Discovery-Tr/NodeMCU_ve_3D_Yazici_Ile_RC_Tank_Yapimi/Foto/Rc Speed Tank (1).jpg

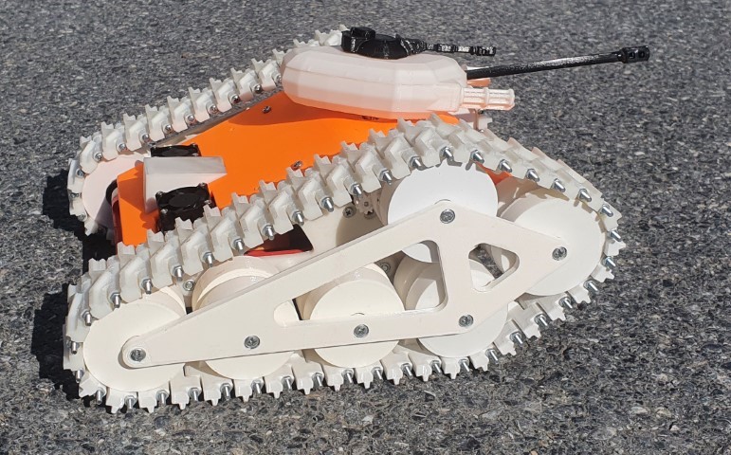
Foto/Rc Speed Tank (1).jpg
