Discovery-Tr/NodeMCU_ve_3D_Yazici_Ile_RC_Tank_Yapimi/Foto/Rc Speed Tank (3).jpeg

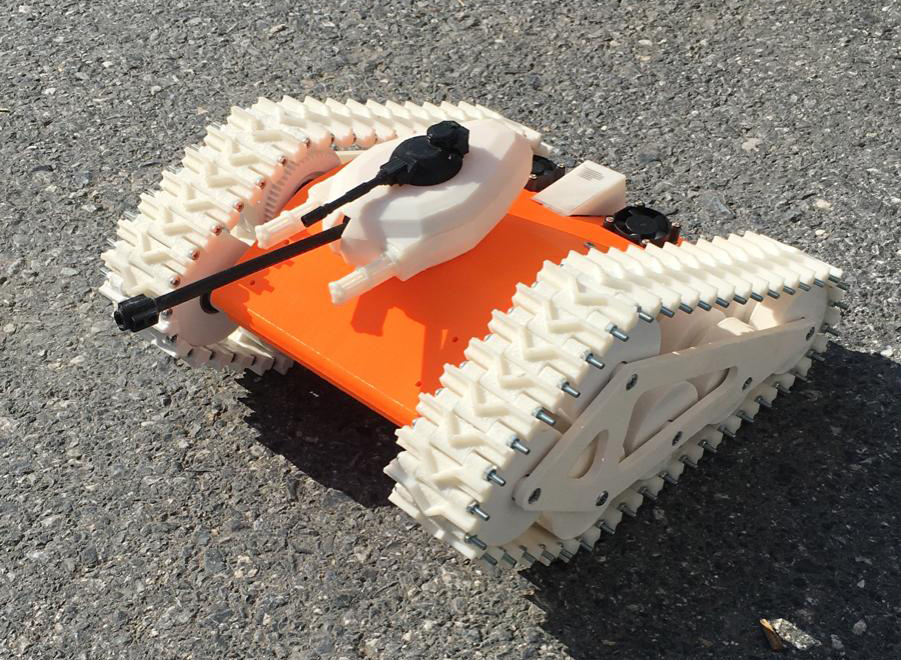
Foto/Rc Speed Tank (3).jpeg
