Discovery-Tr/NodeMCU_ve_3D_Yazici_Ile_RC_Tank_Yapimi/3d/Gövde/Palet Dişlisi.stl

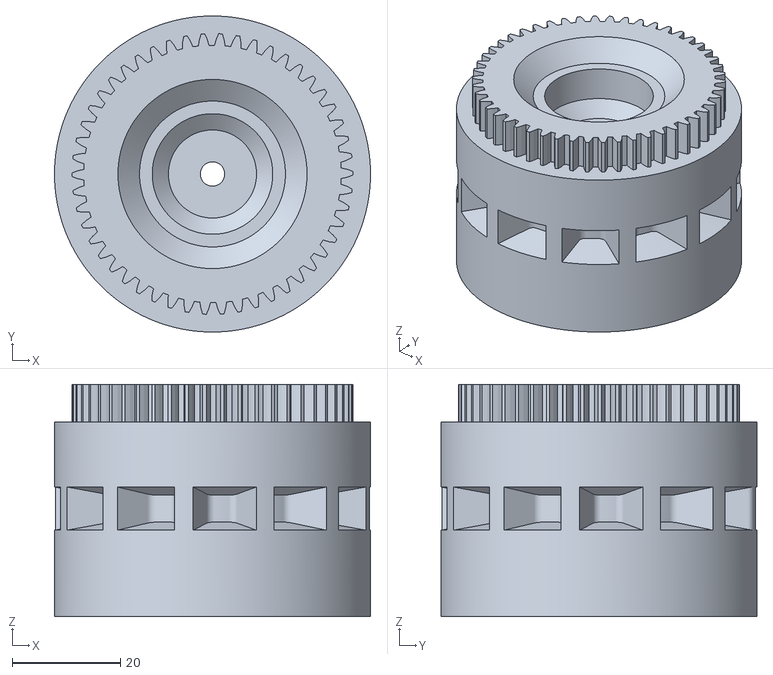
[picture p24: CAD file, 2021-06-29]
3d/Gövde/Palet Dişlisi.stl
58.5 x 58.5 x 43.0
