Discovery-Tr/NodeMCU_ve_3D_Yazici_Ile_RC_Tank_Yapimi/3d/Gövde/Taban Arka.stl

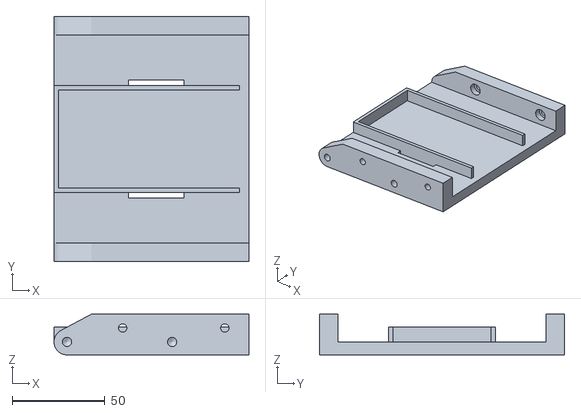
[picture p25: CAD file, 2021-06-29]
3d/Gövde/Taban Arka.stl
105.0 x 132.0 x 22.0
