Discovery-Tr/NodeMCU_ve_3D_Yazici_Ile_RC_Tank_Yapimi/3d/Gövde/motor_disli.stl

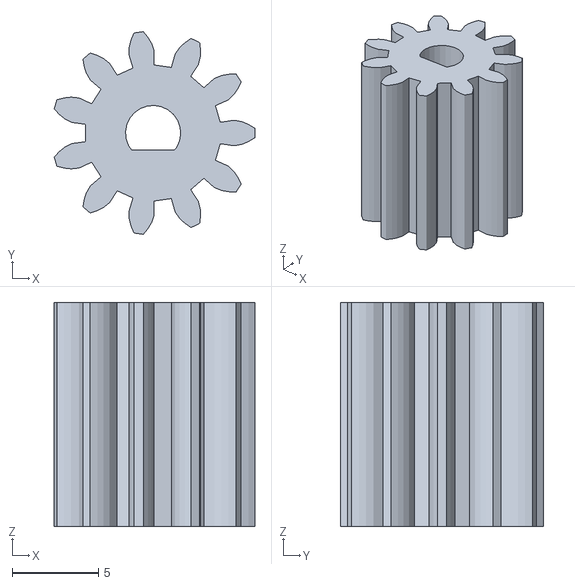
[picture p26: CAD file, 2021-06-29]
3d/Gövde/motor_disli.stl
11.6 x 11.8 x 13.0
