Discovery-Tr/NodeMCU_ve_3D_Yazici_Ile_RC_Tank_Yapimi/3d/Gövde/burun.stl

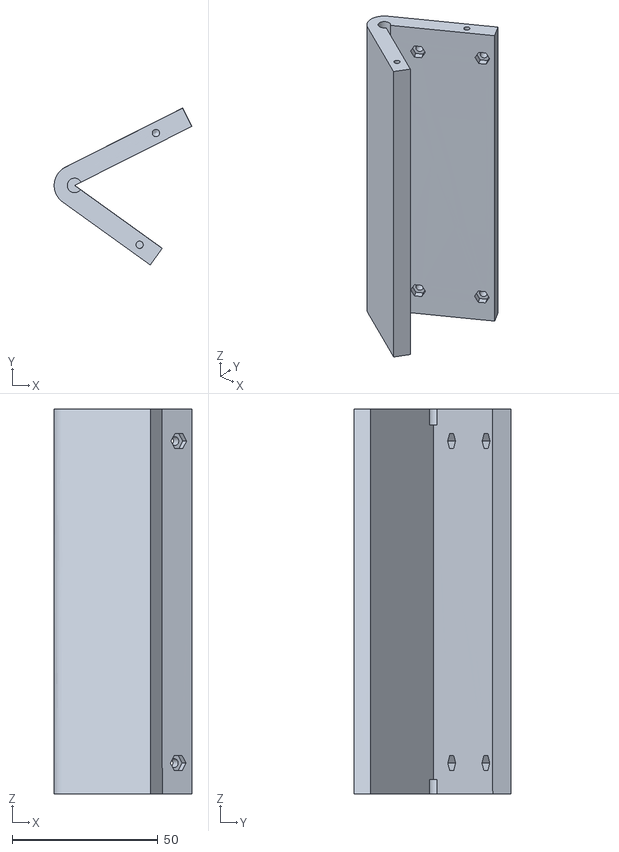
[picture p27: CAD file, 2021-06-29]
3d/Gövde/burun.stl
47.2 x 53.8 x 132.0
